DimitarKV/CBLEmbedded/Simulation/LuggageSimulator/Assets/3DModels/pic.png

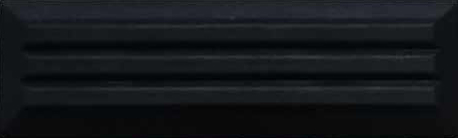
Simulation/LuggageSimulator/Assets/3DModels/pic.png
