DimitarKV/CBLEmbedded/Simulation/LuggageSimulator/Assets/Sprites/18231-5_grobo.png

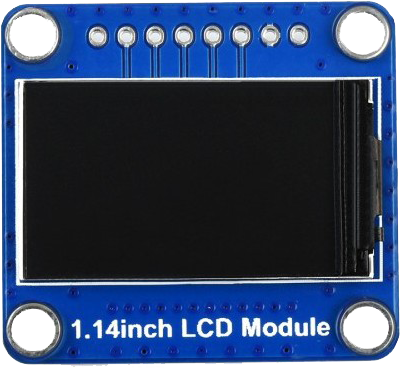
Simulation/LuggageSimulator/Assets/Sprites/18231-5_grobo.png
