DimitarKV/CBLEmbedded/Simulation/LuggageSimulator/Assets/Sprites/Barrier.png

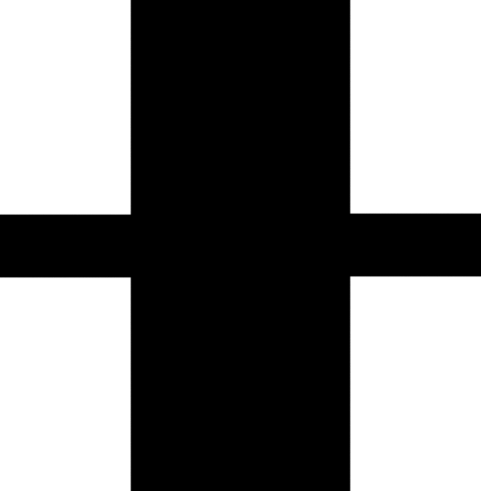
Simulation/LuggageSimulator/Assets/Sprites/Barrier.png
