DimitarKV/CBLEmbedded/Simulation/LuggageSimulator/Assets/Sprites/BarrierNew.png

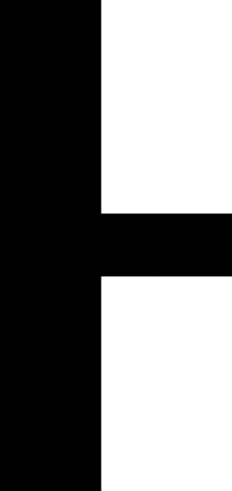
Simulation/LuggageSimulator/Assets/Sprites/BarrierNew.png
