DimitarKV/CBLEmbedded/Simulation/LuggageSimulator/Assets/Sprites/conveyor.png

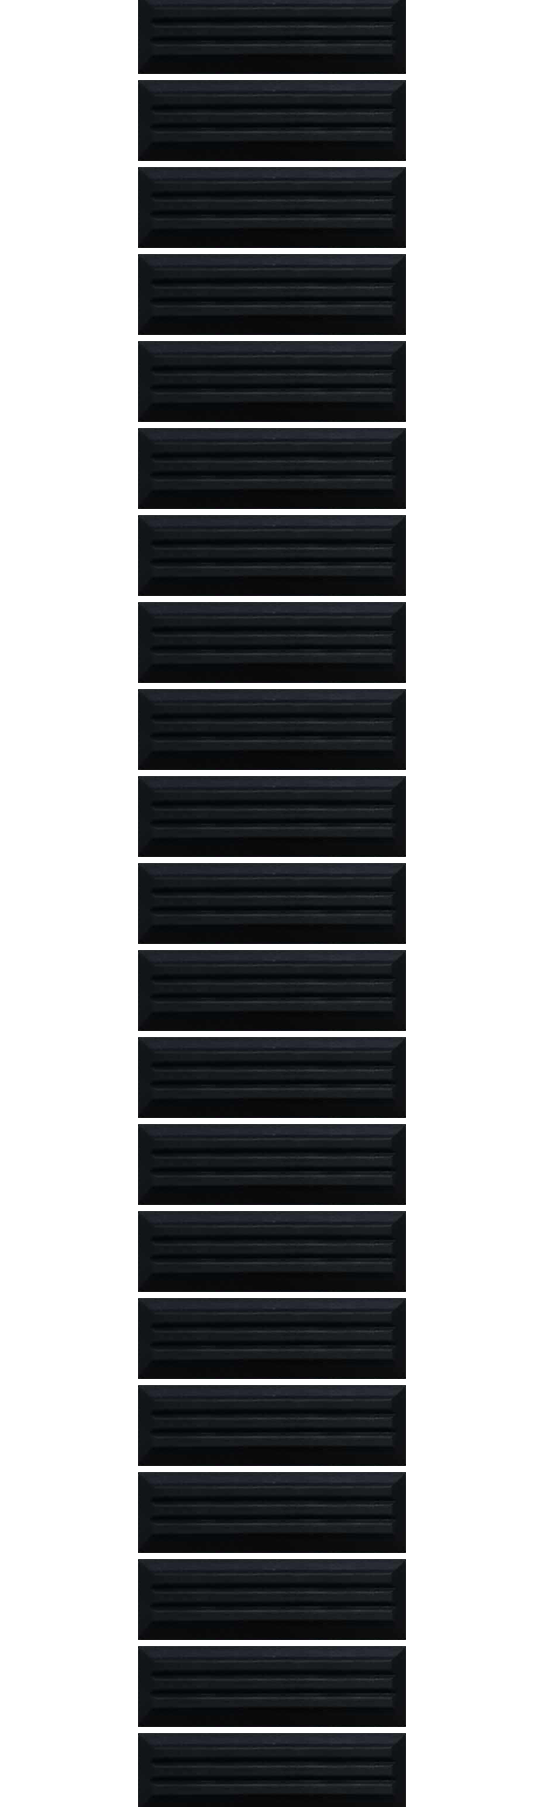
Simulation/LuggageSimulator/Assets/Sprites/conveyor.png
