DimitarKV/CBLEmbedded/Simulation/LuggageSimulator/Assets/Sprites/conveyorHorizontal.png

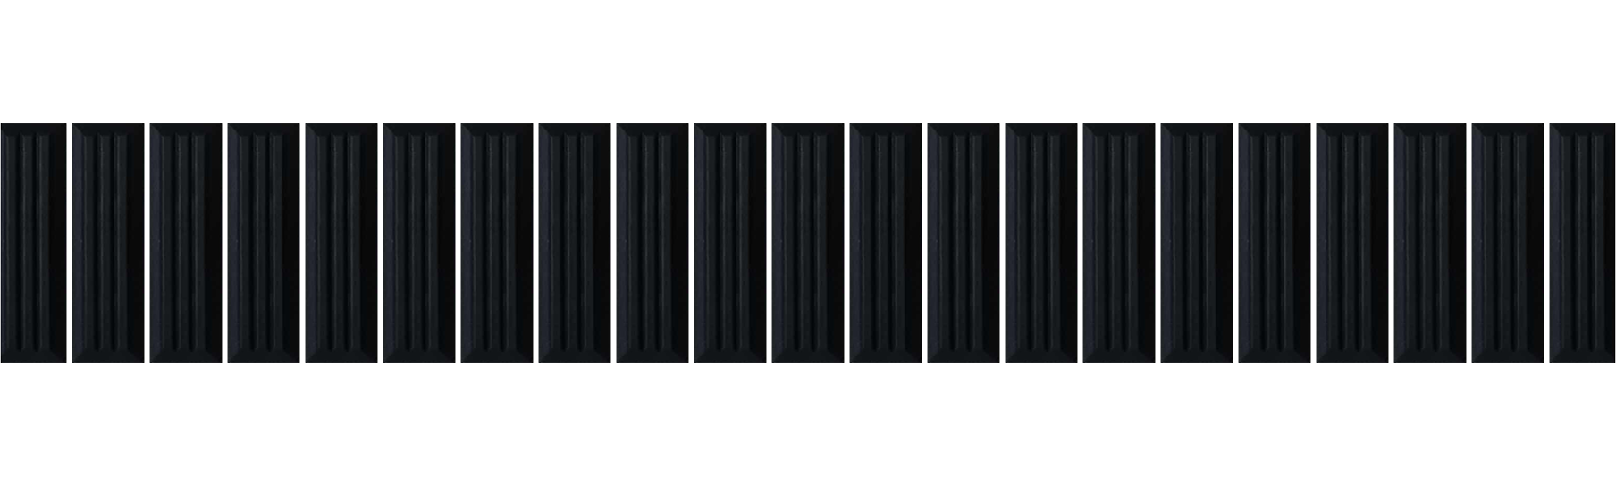
Simulation/LuggageSimulator/Assets/Sprites/conveyorHorizontal.png
