DimitarKV/CBLEmbedded/Printing/Resources/Fischertechnik matching pins. - 4074749/files/wpin_haaks_15.stl

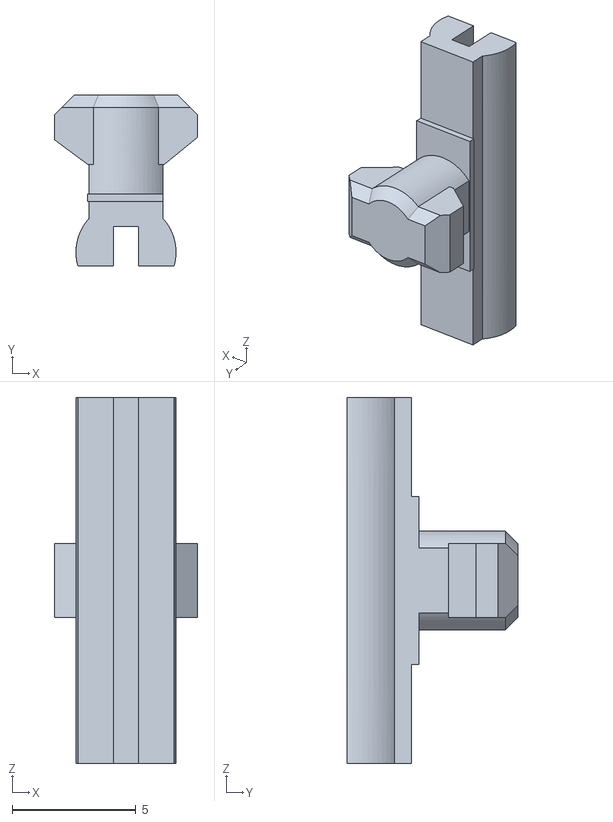
[picture p23: CAD file, 2024-05-15]
Printing/Resources/Fischertechnik matching pins. - 4074749/files/wpin_haaks_15.stl
5.80 x 6.90 x 14.8
