DimitarKV/CBLEmbedded/Printing/Resources/ServoMounts_SMA001_002_TERRN/PN_SMA001-4-24_TERRN.stl

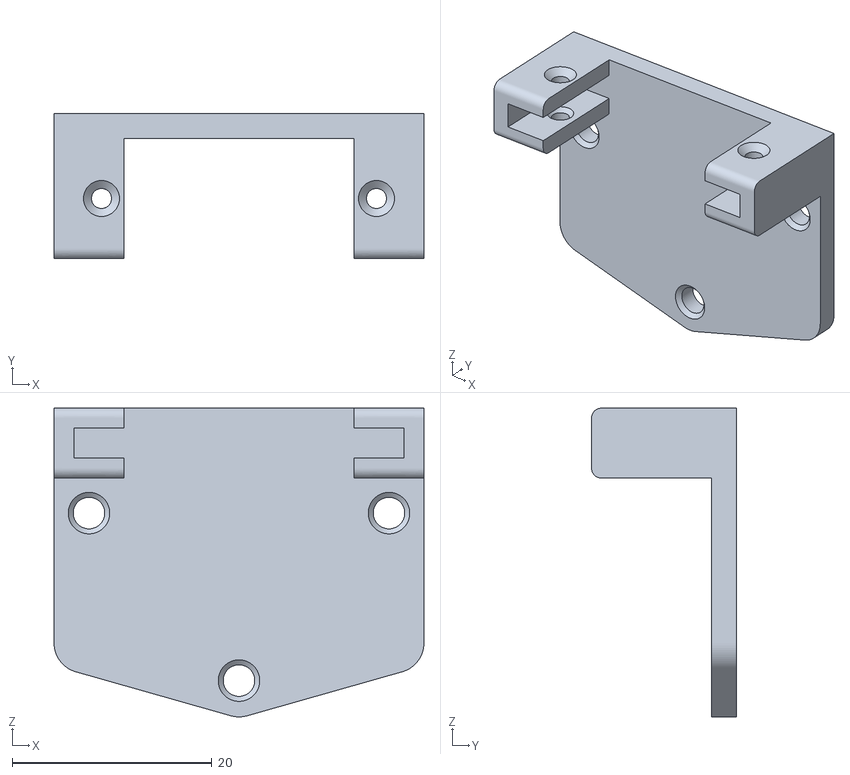
[picture p24: CAD file, 2024-05-15]
Printing/Resources/ServoMounts_SMA001_002_TERRN/PN_SMA001-4-24_TERRN.stl
37.0 x 14.5 x 30.9
