DimitarKV/CBLEmbedded/Printing/Ready/ServoPusherV7/Servo arm overlocker.stl

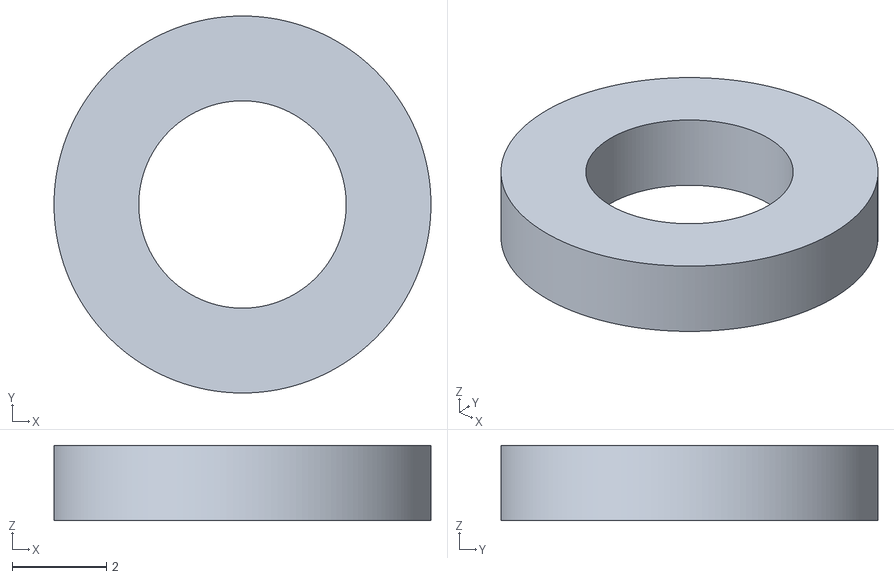
[picture p25: CAD file, 2024-06-09]
Printing/Ready/ServoPusherV7/Servo arm overlocker.stl
8.00 x 8.00 x 1.60
