DimitarKV/CBLEmbedded/Printing/Ready/ServoPusherV7/Servo arm underpin.stl

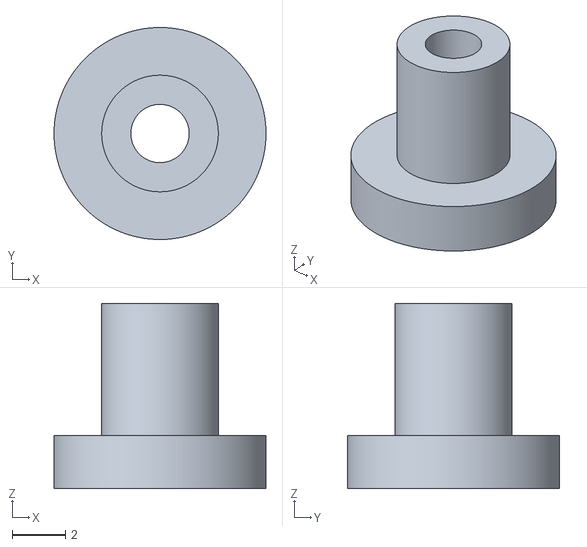
[picture p27: CAD file, 2024-06-09]
Printing/Ready/ServoPusherV7/Servo arm underpin.stl
8.00 x 8.00 x 7.00
