DimitarKV/CBLEmbedded/Printing/Resources/Fischertechnik matching pins. - 4074749/files/pin_9_5_rond.stl

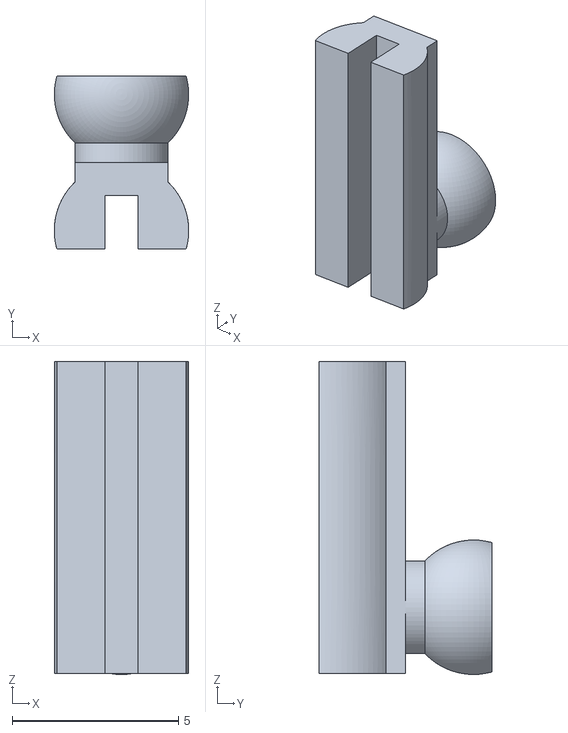
[picture p28: CAD file, 2024-05-15]
Printing/Resources/Fischertechnik matching pins. - 4074749/files/pin_9_5_rond.stl
4.05 x 5.20 x 9.43
