DimitarKV/CBLEmbedded/Printing/Resources/Fischertechnik matching pins. - 4074749/files/pin_9_5_standaard.stl

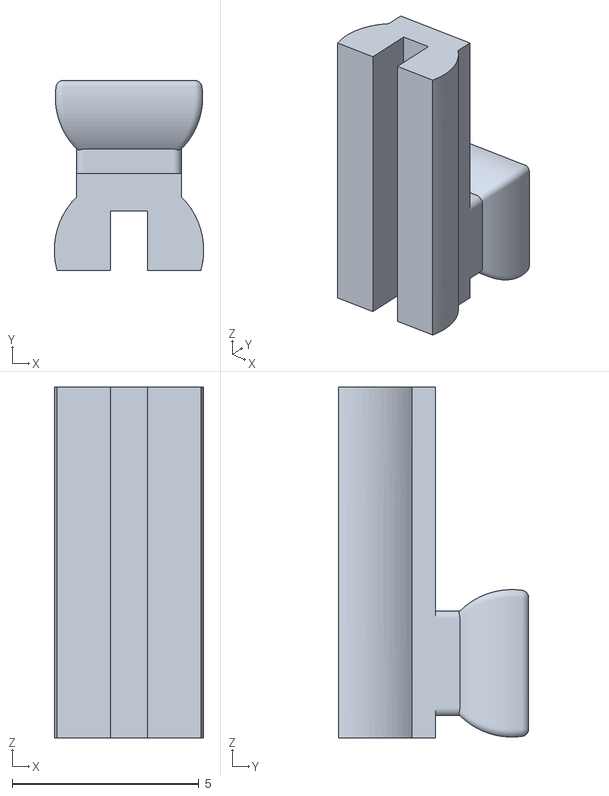
[picture p29: CAD file, 2024-05-15]
Printing/Resources/Fischertechnik matching pins. - 4074749/files/pin_9_5_standaard.stl
4.00 x 5.10 x 9.40
