DimitarKV/CBLEmbedded/Printing/Resources/Fischertechnik matching pins. - 4074749/files/pin_15_standaard.stl

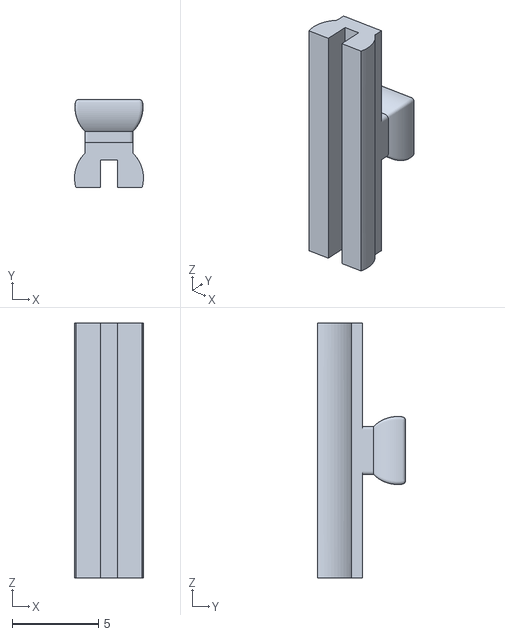
[picture p30: CAD file, 2024-05-15]
Printing/Resources/Fischertechnik matching pins. - 4074749/files/pin_15_standaard.stl
4.00 x 5.10 x 14.8
