DimitarKV/CBLEmbedded/Printing/Resources/Fischertechnik matching pins. - 4074749/images/pin_15_rond.png

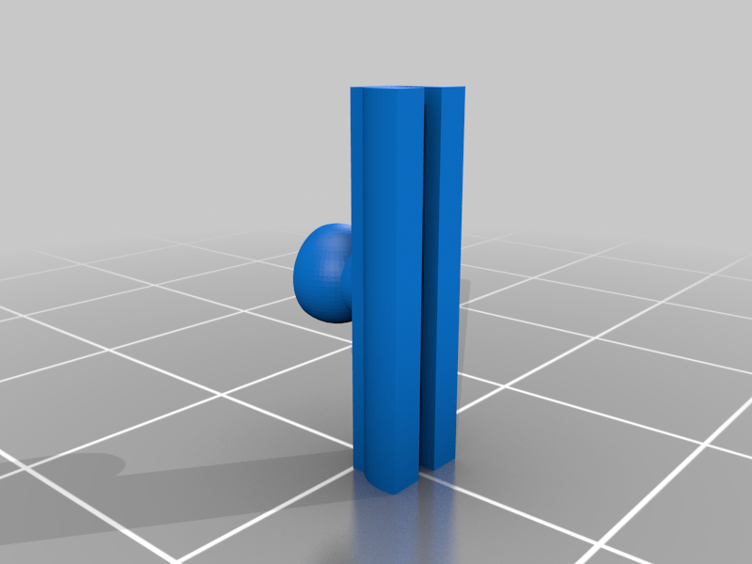
Printing/Resources/Fischertechnik matching pins. - 4074749/images/pin_15_rond.png
