DimitarKV/CBLEmbedded/Printing/Resources/Fischertechnik matching pins. - 4074749/images/pins.jpg

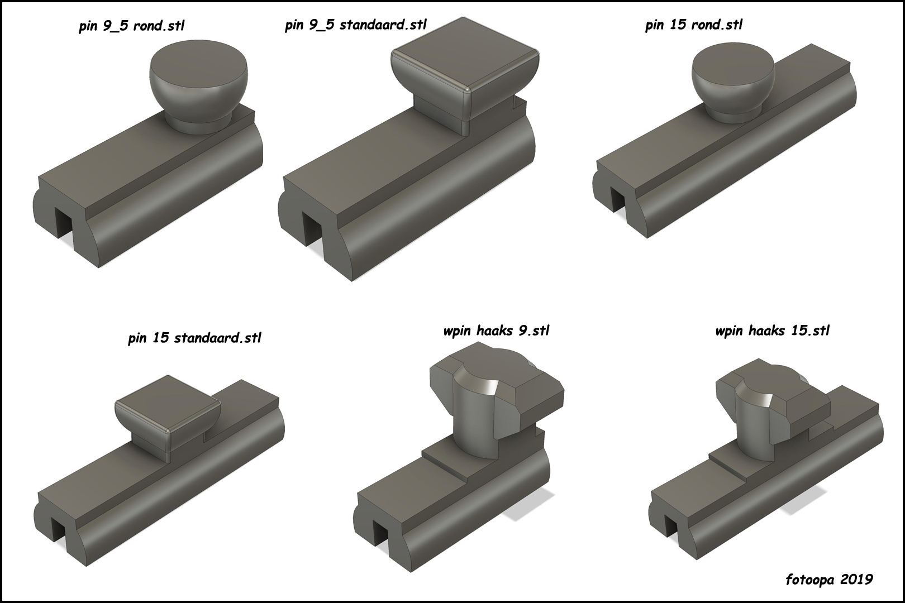
Printing/Resources/Fischertechnik matching pins. - 4074749/images/pins.jpg
