DimitarKV/CBLEmbedded/Printing/Resources/Fischertechnik matching pins. - 4074749/images/wpin_haaks_15.png

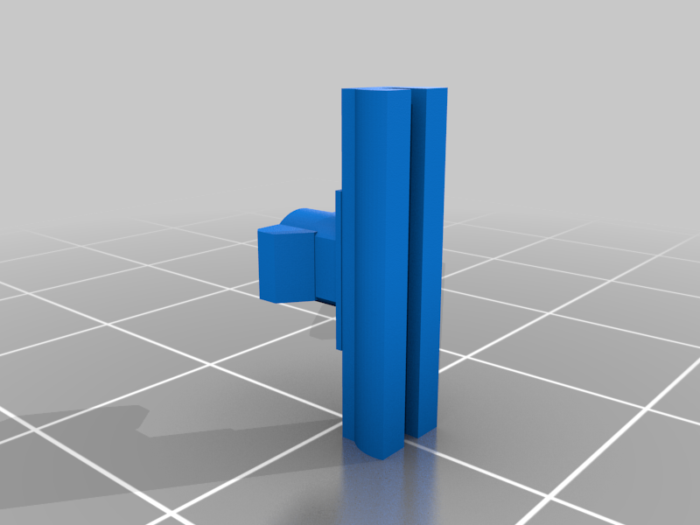
Printing/Resources/Fischertechnik matching pins. - 4074749/images/wpin_haaks_15.png
