DimitarKV/CBLEmbedded/Printing/Resources/Sg90 servo - 4315907/images/Sg90_2020-Apr-26_04-38-33PM-000_CustomizedView27460168344_png.png

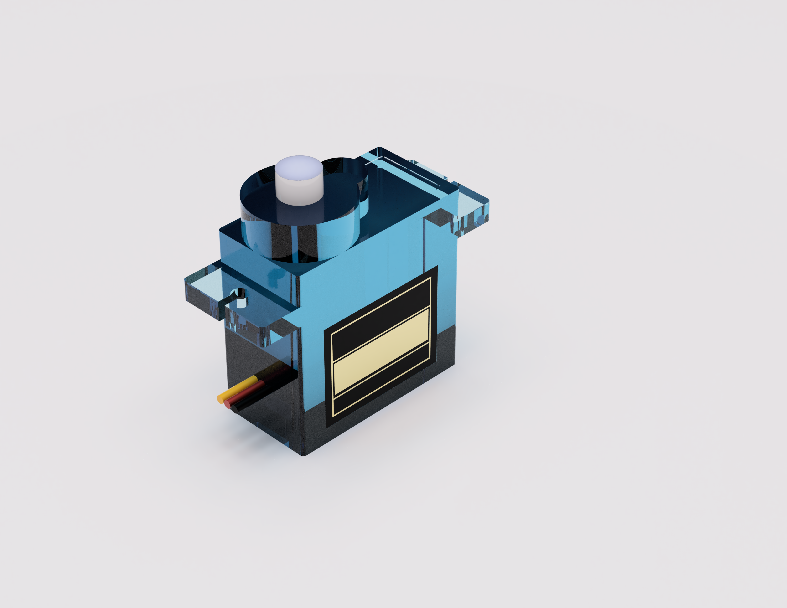
Printing/Resources/Sg90 servo - 4315907/images/Sg90_2020-Apr-26_04-38-33PM-000_CustomizedView27460168344_png.png
