DimitarKV/CBLEmbedded/Printing/Resources/Sg90 servo - 4315907/images/Sg90_2020-Apr-26_04-39-25PM-000_CustomizedView2807987615_png.png

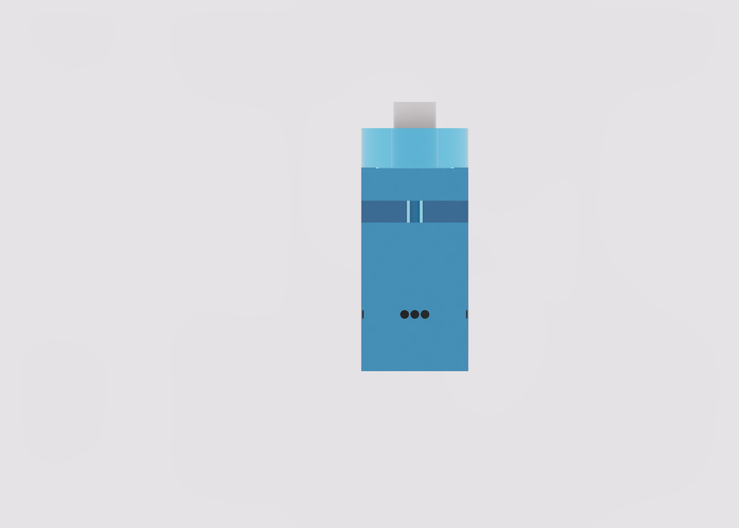
Printing/Resources/Sg90 servo - 4315907/images/Sg90_2020-Apr-26_04-39-25PM-000_CustomizedView2807987615_png.png
