DimitarKV/CBLEmbedded/Printing/Resources/Sg90 servo - 4315907/images/Sg90_2020-Apr-26_04-39-35PM-000_CustomizedView15255391460_png.png

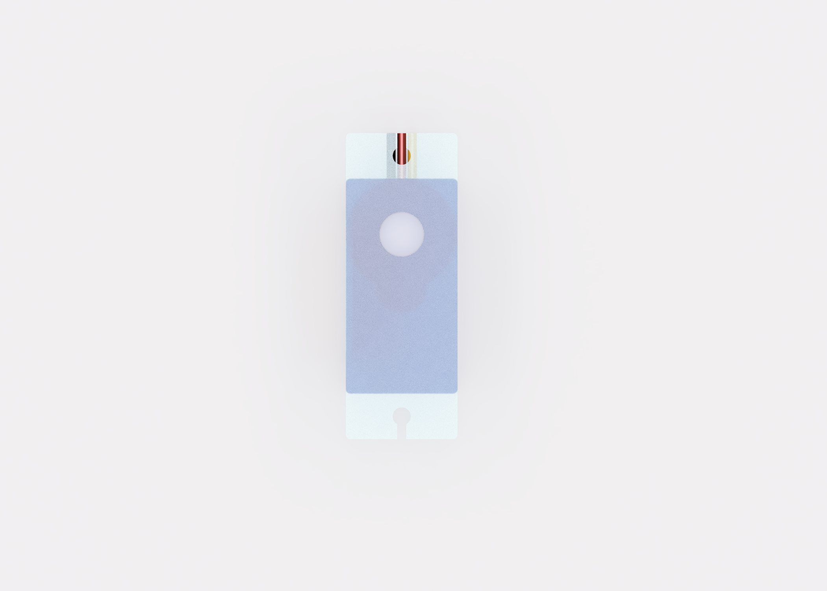
Printing/Resources/Sg90 servo - 4315907/images/Sg90_2020-Apr-26_04-39-35PM-000_CustomizedView15255391460_png.png
