DimitarKV/CBLEmbedded/Printing/Resources/Tower Pro Micro Servo 9g SG90 - 787942/images/2051_servo_tower-pro-sg90.pk2.png

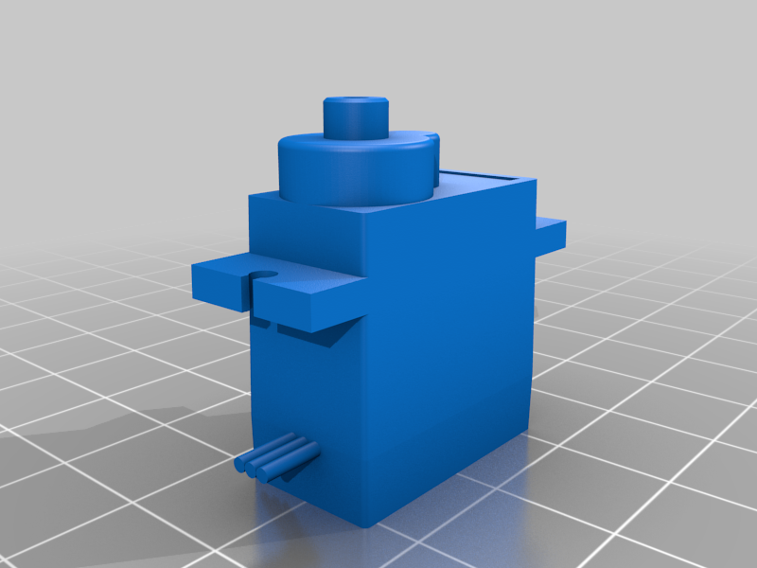
Printing/Resources/Tower Pro Micro Servo 9g SG90 - 787942/images/2051_servo_tower-pro-sg90.pk2.png
