DimitarKV/CBLEmbedded/Printing/Resources/Tower Pro Micro Servo 9g SG90 - 787942/images/servo.JPG

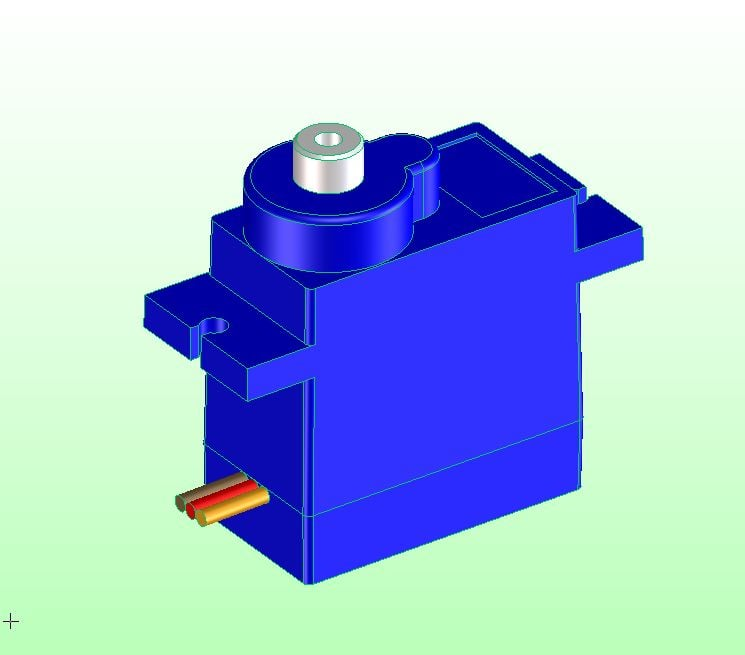
Printing/Resources/Tower Pro Micro Servo 9g SG90 - 787942/images/servo.JPG
